rsgeek/trinus-unofficial-beginners-guide/docs/chapter-00-general/orig/lcd-file-list.jpg

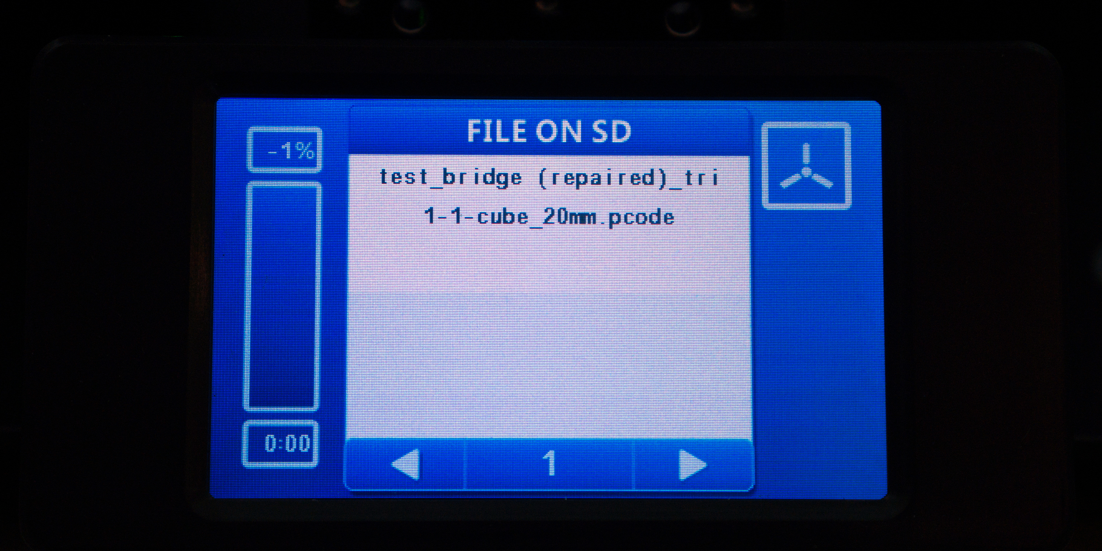
docs/chapter-00-general/orig/lcd-file-list.jpg
