rsgeek/trinus-unofficial-beginners-guide/docs/chapter-00-general/orig/pango-console-sdcard-filelist.png

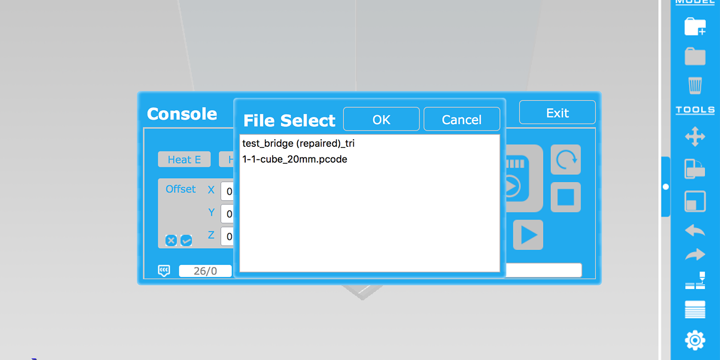
docs/chapter-00-general/orig/pango-console-sdcard-filelist.png
