rsgeek/trinus-unofficial-beginners-guide/docs/chapter-00-general/orig/pango-expert-settings.png

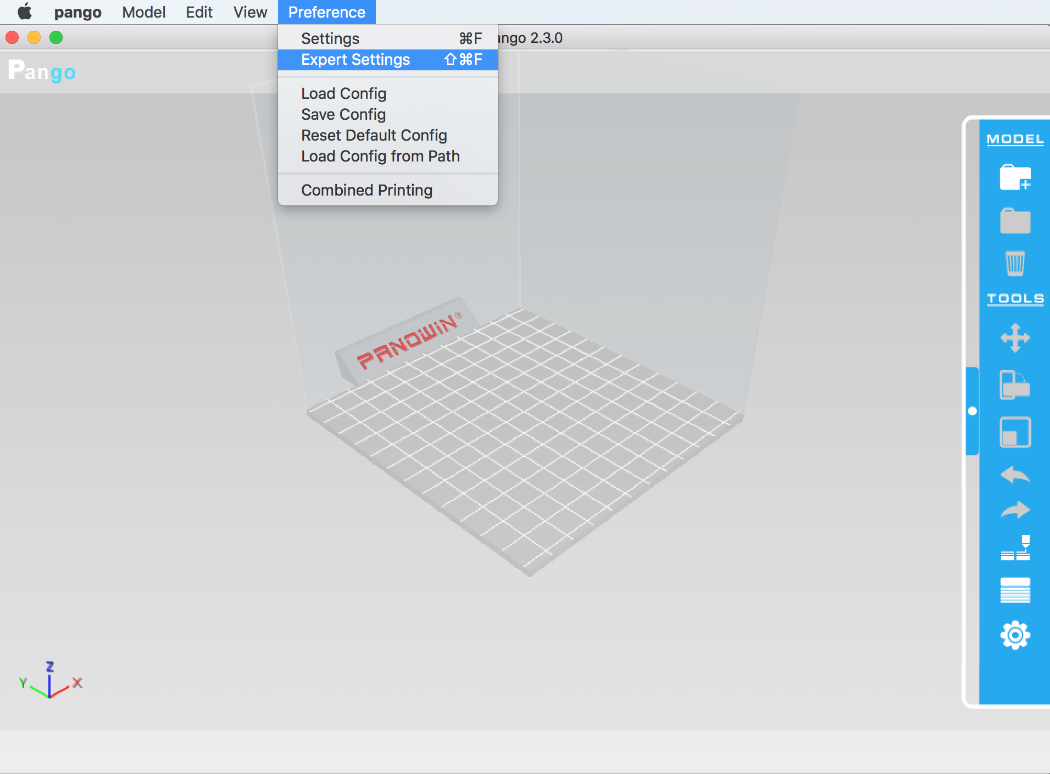
docs/chapter-00-general/orig/pango-expert-settings.png
