rsgeek/trinus-unofficial-beginners-guide/docs/chapter-03-pre-check/img/forums-downloads-essential-files.png

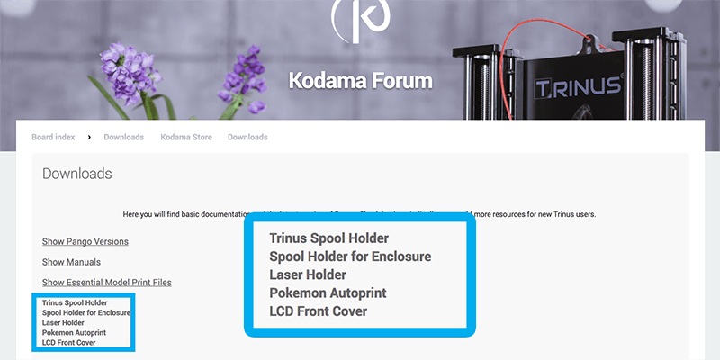
docs/chapter-03-pre-check/img/forums-downloads-essential-files.png
