rsgeek/trinus-unofficial-beginners-guide/docs/chapter-03-pre-check/orig/heated-bed-cable-org-rick-miller.jpg

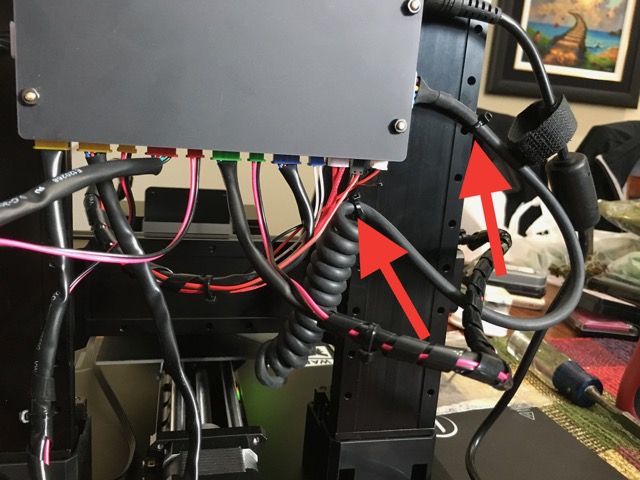
docs/chapter-03-pre-check/orig/heated-bed-cable-org-rick-miller.jpg
