rsgeek/trinus-unofficial-beginners-guide/docs/chapter-06-printing-your-own-models/img/pango-expert-settings-fan-on.png

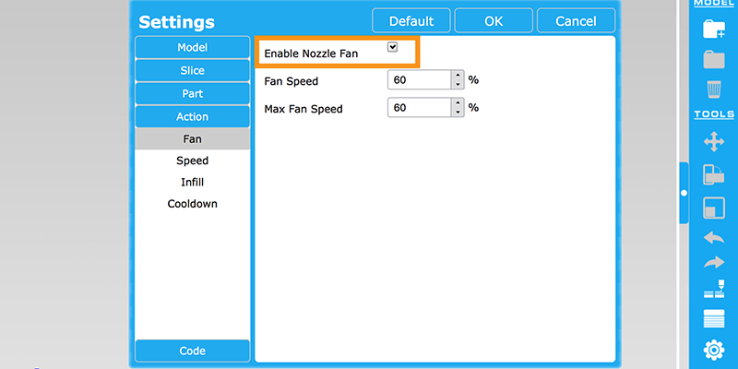
docs/chapter-06-printing-your-own-models/img/pango-expert-settings-fan-on.png
